nbreard/mellia/software/ruche_soft/STM32Cube_FW_WL_V1.1.0/Projects/NUCLEO-WL55JC/Applications/LoRaWAN/LoRaWAN_End_Node/STM32CubeIDE/Sensors/Inc/weight_sensor.h

/*
 * weight_sensor.h
 *
 *  Created on: Mar 30, 2022
 *      Author: nicolas
 */

#ifndef SENSORS_INC_WEIGHT_SENSOR_H_
#define SENSORS_INC_WEIGHT_SENSOR_H_

#include "main.h"
#include "stm32wlxx_hal_spi.h"

#include "sys_sensors.h"
#include "spi.h"

void ADS1232Sensors_Init(sensor_t *sensor_data);
void ADS1232_Read(sensor_t *sensor_data);
void ADS1232_OffsetReset();


#endif /* SENSORS_INC_WEIGHT_SENSOR_H_ */
