nbreard/mellia/software/ruche_soft/STM32Cube_FW_WL_V1.1.0/Projects/NUCLEO-WL55JC/Applications/LoRaWAN/LoRaWAN_End_Node/Core/Src/stm32wlxx_it.c

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

/* Includes ------------------------------------------------------------------*/
#include "main.h"
#include "stm32wlxx_it.h"
/* External variables --------------------------------------------------------*/
extern RTC_HandleTypeDef hrtc;
extern SUBGHZ_HandleTypeDef hsubghz;
extern DMA_HandleTypeDef hdma_usart2_tx;
extern UART_HandleTypeDef huart2;
/******************************************************************************/
/*           Cortex Processor Interruption and Exception Handlers          */
/******************************************************************************/
/**
  * @brief This function handles Non maskable interrupt.
  */
void NMI_Handler(void)
{
  /* USER CODE BEGIN NonMaskableInt_IRQn 1 */
  while (1)
  {
  }
  /* USER CODE END NonMaskableInt_IRQn 1 */
}

/**
  * @brief This function handles Hard fault interrupt.
  */
void HardFault_Handler(void)
{
  /* USER CODE BEGIN HardFault_IRQn 0 */
	__asm volatile
	    (
	        " tst lr, #4                                                \n"
	        " ite eq                                                    \n"
	        " mrseq r0, msp                                             \n"
	        " mrsne r0, psp                                             \n"
	        " ldr r1, [r0, #24]                                         \n"
	        " ldr r2, handler2_address_const                            \n"
	        " bx r2                                                     \n"
	        " handler2_address_const: .word prvGetRegistersFromStack    \n"
	    );
  /* USER CODE END HardFault_IRQn 0 */
  while (1)
  {
  }
}

/**
  * @brief This function handles Memory management fault.
  */
void MemManage_Handler(void)
{
  while (1)
  {
  }
}

/**
  * @brief This function handles Prefetch fault, memory access fault.
  */
void BusFault_Handler(void)
{
  while (1)
  {
  }
}

/**
  * @brief This function handles Undefined instruction or illegal state.
  */
void UsageFault_Handler(void)
{
  while (1)
  {
  }
}

/**
  * @brief This function handles System service call via SWI instruction.
  */
void SVC_Handler(void)
{
}

/**
  * @brief This function handles Debug monitor.
  */
void DebugMon_Handler(void)
{
}

/**
  * @brief This function handles Pendable request for system service.
  */
void PendSV_Handler(void)
{
}

/**
  * @brief This function handles System tick timer.
  */
void SysTick_Handler(void)
{
  /* USER CODE BEGIN SysTick_IRQn 0 */
	uwTick++;

  /* USER CODE END SysTick_IRQn 0 */
}

/******************************************************************************/
/* STM32WLxx Peripheral Interrupt Handlers                                    */
/* Add here the Interrupt Handlers for the used peripherals.                  */
/* For the available peripheral interrupt handler names,                      */
/* please refer to the startup file (startup_stm32wlxx.s).                    */
/******************************************************************************/

/**
  * @brief This function handles RTC Tamper, RTC TimeStamp, LSECSS and RTC SSRU Interrupts.
  */
void TAMP_STAMP_LSECSS_SSRU_IRQHandler(void)
{
  HAL_RTCEx_SSRUIRQHandler(&hrtc);
}

/**
  * @brief This function handles EXTI Line 0 Interrupt.
  */
void EXTI0_IRQHandler(void)
{
  HAL_GPIO_EXTI_IRQHandler(GPIO_PIN_0);
}

/**
  * @brief This function handles EXTI Line 1 Interrupt.
  */
void EXTI1_IRQHandler(void)
{
  HAL_GPIO_EXTI_IRQHandler(GPIO_PIN_1);
}

/**
  * @brief This function handles DMA1 Channel 5 Interrupt.
  */
void DMA1_Channel5_IRQHandler(void)
{
  HAL_DMA_IRQHandler(&hdma_usart2_tx);
}

/**
  * @brief This function handles USART2 Interrupt.
  */
void USART2_IRQHandler(void)
{
  HAL_UART_IRQHandler(&huart2);
}

/**
  * @brief This function handles RTC Alarms (A and B) Interrupt.
  */
void RTC_Alarm_IRQHandler(void)
{
  HAL_RTC_AlarmIRQHandler(&hrtc);
}

/**
  * @brief This function handles SUBGHZ Radio Interrupt.
  */
void SUBGHZ_Radio_IRQHandler(void)
{
  HAL_SUBGHZ_IRQHandler(&hsubghz);
}

/* USER CODE BEGIN 1 */
void prvGetRegistersFromStack( uint32_t *pulFaultStackAddress )
{
/* These are volatile to try and prevent the compiler/linker optimising them
away as the variables never actually get used.  If the debugger won't show the
values of the variables, make them global my moving their declaration outside
of this function. */
volatile uint32_t r0;
volatile uint32_t r1;
volatile uint32_t r2;
volatile uint32_t r3;
volatile uint32_t r12;
volatile uint32_t lr; /* Link register. */
volatile uint32_t pc; /* Program counter. */
volatile uint32_t psr;/* Program status register. */

    r0 = pulFaultStackAddress[ 0 ];
    r1 = pulFaultStackAddress[ 1 ];
    r2 = pulFaultStackAddress[ 2 ];
    r3 = pulFaultStackAddress[ 3 ];

    r12 = pulFaultStackAddress[ 4 ];
    lr = pulFaultStackAddress[ 5 ];
    pc = pulFaultStackAddress[ 6 ];
    psr = pulFaultStackAddress[ 7 ];

    /* When the following line is hit, the variables contain the register values. */
    for( ;; );
}
/* USER CODE END 1 */
/************************ (C) COPYRIGHT STMicroelectronics *****END OF FILE****/
