nbreard/mellia/software/ruche_soft/STM32Cube_FW_WL_V1.1.0/Projects/NUCLEO-WL55JC/Applications/LoRaWAN/LoRaWAN_End_Node/Core/Src/spi.c

/* USER CODE BEGIN Header */
/**
  ******************************************************************************
  * @file         spi.c
  * @brief        This file provides code for the MSP Initialization
  *               and de-Initialization codes.
  ******************************************************************************

/* Includes ------------------------------------------------------------------*/
#include "spi.h"
SPI_HandleTypeDef hspi2;

void MX_SPI2_Init(void)
{

  /* SPI2 parameter configuration*/
  hspi2.Instance = SPI2;
  hspi2.Init.Mode = SPI_MODE_MASTER;
  hspi2.Init.Direction = SPI_DIRECTION_2LINES;
  hspi2.Init.DataSize = SPI_DATASIZE_8BIT;
  hspi2.Init.CLKPolarity = SPI_POLARITY_HIGH;
  hspi2.Init.CLKPhase = SPI_PHASE_2EDGE;
  hspi2.Init.NSS = SPI_NSS_SOFT;
  hspi2.Init.BaudRatePrescaler = SPI_BAUDRATEPRESCALER_2;
  hspi2.Init.FirstBit = SPI_FIRSTBIT_MSB;
  hspi2.Init.TIMode = SPI_TIMODE_DISABLE;
  hspi2.Init.CRCCalculation = SPI_CRCCALCULATION_DISABLE;
  hspi2.Init.CRCPolynomial = 7;
  hspi2.Init.CRCLength = SPI_CRC_LENGTH_DATASIZE;
  hspi2.Init.NSSPMode = SPI_NSS_PULSE_DISABLE;
  if (HAL_SPI_Init(&hspi2) != HAL_OK)
  {
    Error_Handler();
  }
}

/**
* @brief SPI MSP Initialization
* This function configures the hardware resources used in this example
* @param hspi: SPI handle pointer
* @retval None
*/
void HAL_SPI_MspInit(SPI_HandleTypeDef* hspi)
{
  GPIO_InitTypeDef GPIO_InitStruct = {0};
  RCC_PeriphCLKInitTypeDef PeriphClkInitStruct = {0};
  if(hspi->Instance==SPI2)
  {
  /** Initializes the peripherals clocks
  */
    PeriphClkInitStruct.PeriphClockSelection = RCC_PERIPHCLK_I2S2;
    PeriphClkInitStruct.I2s2ClockSelection = RCC_I2S2CLKSOURCE_HSI;
    if (HAL_RCCEx_PeriphCLKConfig(&PeriphClkInitStruct) != HAL_OK)
    {
      Error_Handler();
    }

    /* Peripheral clock enable */
    __HAL_RCC_SPI2_CLK_ENABLE();

    __HAL_RCC_GPIOB_CLK_ENABLE();
    __HAL_RCC_GPIOA_CLK_ENABLE();
    /**SPI2 GPIO Configuration
    PB14     ------> SPI2_MISO
    PA10     ------> SPI2_MOSI
    PB13     ------> SPI2_SCK
    */
    GPIO_InitStruct.Pin = GPIO_PIN_14|GPIO_PIN_13;
    GPIO_InitStruct.Mode = GPIO_MODE_AF_PP;
    GPIO_InitStruct.Pull = GPIO_NOPULL;
    GPIO_InitStruct.Speed = GPIO_SPEED_FREQ_LOW;
    GPIO_InitStruct.Alternate = GPIO_AF5_SPI2;
    HAL_GPIO_Init(GPIOB, &GPIO_InitStruct);

    GPIO_InitStruct.Pin = GPIO_PIN_10;
    GPIO_InitStruct.Mode = GPIO_MODE_AF_PP;
    GPIO_InitStruct.Pull = GPIO_NOPULL;
    GPIO_InitStruct.Speed = GPIO_SPEED_FREQ_LOW;
    GPIO_InitStruct.Alternate = GPIO_AF5_SPI2;
    HAL_GPIO_Init(GPIOA, &GPIO_InitStruct);

  /* USER CODE BEGIN SPI2_MspInit 1 */
    /*Configure GPIO pin Output Level */

    /*Configure GPIO pins : BME_NSS_Pin ADS_NSS_Pin */
    GPIO_InitStruct.Pin = BME_NSS_Pin|ADS_NSS_Pin;
    GPIO_InitStruct.Mode = GPIO_MODE_OUTPUT_PP;
    GPIO_InitStruct.Pull = GPIO_NOPULL;
    GPIO_InitStruct.Speed = GPIO_SPEED_FREQ_LOW;
    HAL_GPIO_Init(GPIOB, &GPIO_InitStruct);

    HAL_GPIO_WritePin(GPIOB, BME_NSS_Pin|ADS_NSS_Pin, GPIO_PIN_SET);

  /* USER CODE END SPI2_MspInit 1 */
  }

}

/**
* @brief SPI MSP De-Initialization
* This function freeze the hardware resources used in this example
* @param hspi: SPI handle pointer
* @retval None
*/
void HAL_SPI_MspDeInit(SPI_HandleTypeDef* hspi)
{
  if(hspi->Instance==SPI2)
  {
    /* Peripheral clock disable */
    __HAL_RCC_SPI2_CLK_DISABLE();

    /**SPI2 GPIO Configuration
    PB14     ------> SPI2_MISO
    PA10     ------> SPI2_MOSI
    PB13     ------> SPI2_SCK
    */
    HAL_GPIO_DeInit(GPIOB, GPIO_PIN_14|GPIO_PIN_13);

    HAL_GPIO_DeInit(GPIOA, GPIO_PIN_10);

  }

}
