nbreard/mellia/software/ruche_soft/STM32Cube_FW_WL_V1.1.0/Projects/NUCLEO-WL55JC/Applications/LoRaWAN/LoRaWAN_End_Node/Core/Inc/spi.h

/*
 * spi.h
 *
 *  Created on: Mar 23, 2022
 *      Author: nicolas
 */

#ifndef APPLICATION_USER_CORE_SPI_H_
#define APPLICATION_USER_CORE_SPI_H_

#include "main.h"


#define BME_NSS_Pin GPIO_PIN_7
#define BME_NSS_GPIO_Port GPIOB
#define ADS_NSS_Pin GPIO_PIN_6
#define ADS_NSS_GPIO_Port GPIOB

extern SPI_HandleTypeDef hspi2;

void MX_SPI2_Init(void);
void HAL_SPI_MspInit(SPI_HandleTypeDef* hspi);
void HAL_SPI_MspDeInit(SPI_HandleTypeDef* hspi);

#endif /* APPLICATION_USER_CORE_SPI_H_ */
