nbreard/mellia/software/ruche_soft/STM32Cube_FW_WL_V1.1.0/Projects/NUCLEO-WL55JC/Applications/LoRaWAN/LoRaWAN_End_Node/Core/Inc/spi_if.h

/*
 * spi_if.h
 *
 *  Created on: Mar 23, 2022
 *      Author: nicolas
 */

#ifndef APPLICATION_USER_CORE_SPI_IF_H_
#define APPLICATION_USER_CORE_SPI_IF_H_

#include "stdint.h"

int8_t user_spi_read(uint8_t dev_id, uint8_t reg_addr, uint8_t *reg_data, uint16_t len);
int8_t user_spi_write(uint8_t dev_id, uint8_t reg_addr, uint8_t *reg_data, uint16_t len);


#endif /* APPLICATION_USER_CORE_SPI_IF_H_ */
