nbreard/mellia/software/weather_shield/Core/Src/i2c_if.c

#include "i2c_if.h"
#include "i2c.h"



int8_t user_i2c_read(uint8_t dev_id, uint8_t reg_addr, uint8_t *reg_data, uint16_t len)
{
	int8_t rslt = 0; /* Return 0 for Success, non-zero for failure */
	uint32_t error=0;
	uint8_t read_addr=(dev_id<<1);




		rslt=HAL_I2C_Mem_Read(&hi2c1,(uint16_t)read_addr,reg_addr,I2C_MEMADD_SIZE_8BIT,reg_data, len, 1000);
	/*
	 * The parameter dev_id can be used as a variable to store the I2C address of the device
	 */

	/*
	 * Data on the bus should be like
	 * |------------+---------------------|
	 * | I2C action | Data                |
	 * |------------+---------------------|
	 * | Start      | -                   |
	 * | Write      | (reg_addr)          |
	 * | Stop       | -                   |
	 * | Start      | -                   |
	 * | Read       | (reg_data[0])       |
	 * | Read       | (....)              |
	 * | Read       | (reg_data[len - 1]) |
	 * | Stop       | -                   |
	 * |------------+---------------------|
	 */

	return rslt;
}


int8_t user_i2c_write(uint8_t dev_id, uint8_t reg_addr, uint8_t *reg_data, uint16_t len)
{
	int8_t rslt = 0; /* Return 0 for Success, non-zero for failure */

	uint8_t write_addr=(dev_id<<1);
	rslt=HAL_I2C_Mem_Write(&hi2c1,(uint16_t)write_addr,reg_addr,I2C_MEMADD_SIZE_8BIT,reg_data, len, 1000);

	/*
	 * The parameter dev_id can be used as a variable to store the I2C address of the device
	 */

	/*
	 * Data on the bus should be like
	 * |------------+---------------------|
	 * | I2C action | Data                |
	 * |------------+---------------------|
	 * | Start      | -                   |
	 * | Write      | (reg_addr)          |
	 * | Write      | (reg_data[0])       |
	 * | Write      | (....)              |
	 * | Write      | (reg_data[len - 1]) |
	 * | Stop       | -                   |
	 * |------------+---------------------|
	 */

	return rslt;
}
